Kushal-Sachdeva78/K.A.D-Ballers-Genius-Olympiad/Photos/Robot Image 5.jpeg

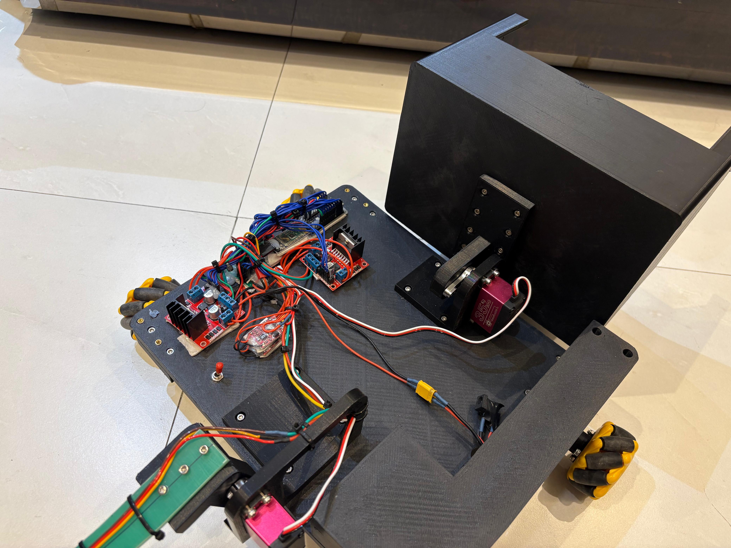
Photos/Robot Image 5.jpeg
