Kushal-Sachdeva78/K.A.D-Ballers-Genius-Olympiad/3D Models/lmotormountbase.SLDPRT

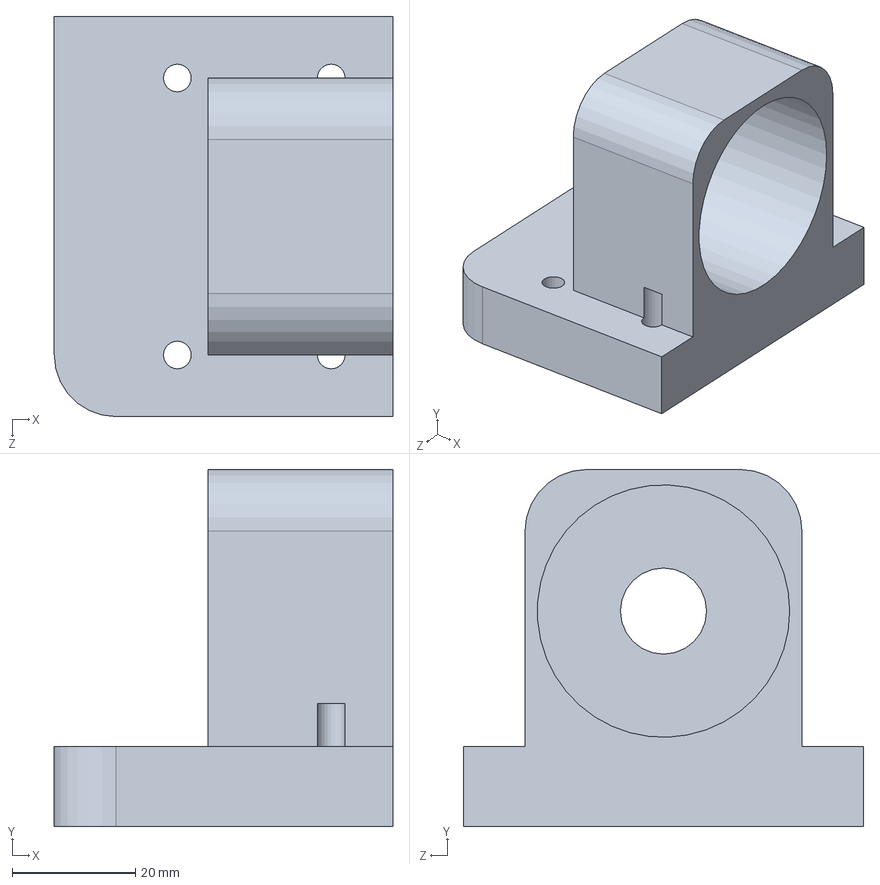
[picture p31: CAD file, 2026-02-26]
3D Models/lmotormountbase.SLDPRT
55.0 x 58.0 x 65.0 mm
