Kushal-Sachdeva78/K.A.D-Ballers-Genius-Olympiad/3D Models/robocarbase.SLDPRT

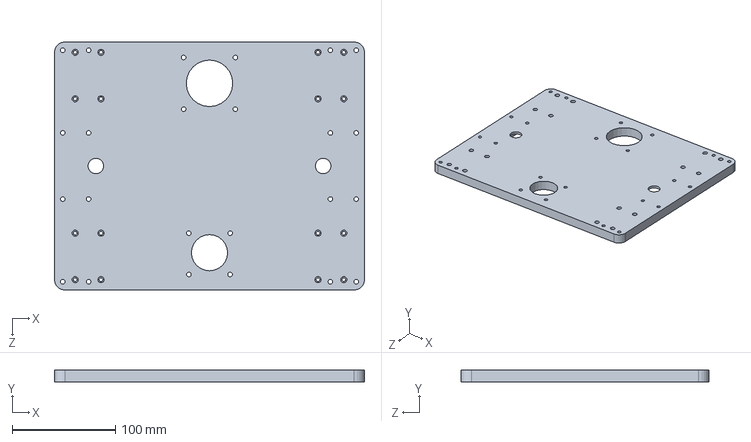
[picture p32: CAD file, 2026-02-26]
3D Models/robocarbase.SLDPRT
300.0 x 12.0 x 240.0 mm
