Kushal-Sachdeva78/K.A.D-Ballers-Genius-Olympiad/3D Models/servoholdballholdercase.SLDPRT

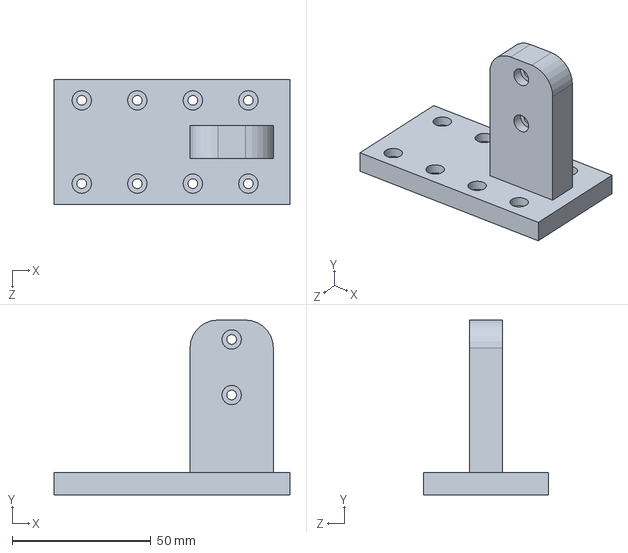
[picture p33: CAD file, 2026-02-26]
3D Models/servoholdballholdercase.SLDPRT
85.0 x 63.0 x 45.0 mm
